sitlesh/4-Channel-Industrial-Isolated-Input-Board/Draft1.asc

D1: LED
R1: res; 1.2K
R2: res; 4.7K
U1: PC817A
V1: voltage; 24V
V2: voltage; 3.3V
Named nets: 0
.tran 10m
